Felteshobbies/moonlamp/firmware/tools/i18n_tests.py

"""German -> English replacements for the test scripts. Data table only."""

PAIRS = [
    # --- shared across the suite
    ('"Alle Pruefungen bestanden."', '"All checks passed."'),
    ('"FEHLGESCHLAGEN: %s" % ", ".join(FAILED)', '"FAILED: %s" % ", ".join(FAILED)'),
    ('"FEHLGESCHLAGEN: %d Pruefungen -> %s" % (len(FAILED), ", ".join(FAILED))',
     '"FAILED: %d checks -> %s" % (len(FAILED), ", ".join(FAILED))'),
    ('"FEHLER"', '"FAILED"'),
    ('"FEHLER: %r != %r"', '"FAILED: %r != %r"'),
    ('"  %-46s FEHLER: keine Anfrage verarbeitet"',
     '"  %-46s FAILED: no request was handled"'),

    # --- test_ephemeris.py
    ('"""Prueft die Ephemeride gegen bekannte astronomische Groessen.\n\n'
     'Laeuft am PC mit CPython, ohne Pico:\n'
     '    python firmware\\\\tests\\\\test_ephemeris.py\n"""',
     '"""Check the ephemeris against known astronomical quantities.\n\n'
     'Runs on a PC under CPython, no Pico needed:\n'
     '    python firmware\\\\tests\\\\test_ephemeris.py\n"""'),
    ('"1. Kalenderrechnung"', '"1. Calendar arithmetic"'),
    ('# J2000.0 ist per Definition der 1.1.2000 12:00 UT = JD 2451545.0',
     '# J2000.0 is by definition 2000-01-01 12:00 UT = JD 2451545.0'),
    ('"JD von 2000-01-01 12:00 UT"', '"JD of 2000-01-01 12:00 UT"'),
    ('# Rueckrechnung muss dasselbe Datum liefern',
     '# Converting back must give the same date'),
    ('"Hin- und Rueckrechnung %s"', '"round trip %s"'),
    ('"2. Sonne: Tagundnachtgleichen und Sonnenwenden"',
     '"2. Sun: equinoxes and solstices"'),
    ('# Zur Fruehlings-Tagundnachtgleiche ist die ekliptikale Laenge der Sonne 0 Grad,\n'
     '# zur Herbst-Tagundnachtgleiche 180. Die Termine sind kalendarisch bekannt.',
     '# At the March equinox the sun\'s ecliptic longitude is 0 degrees, at the\n'
     '# September equinox 180. The dates are known from the calendar.'),
    ('"Fruehlingsanfang 2026-03-20 14:46 UT"', '"March equinox 2026-03-20 14:46 UT"'),
    ('"Herbstanfang     2026-09-23 00:05 UT"', '"September equinox 2026-09-23 00:05 UT"'),
    ('"Sommersonnenwende 2026-06-21 08:24 UT"', '"June solstice 2026-06-21 08:24 UT"'),
    ('"Wintersonnenwende 2026-12-21 20:50 UT"', '"December solstice 2026-12-21 20:50 UT"'),
    ('"  %-46s Laenge %8.3f Grad, Abweichung %+6.3f  %s"',
     '"  %-46s longitude %8.3f deg, error %+6.3f  %s"'),
    ('"3. Mond: Bahngroessen ueber 20 Jahre"', '"3. Moon: orbital quantities over 20 years"'),
    ('"Entfernung Perigaeum..Apogaeum"', '"distance perigee..apogee"'),
    ('# Mittlere siderische Bewegung: 360 Grad in 27.32166 Tagen',
     '# Mean sidereal motion: 360 degrees in 27.32166 days'),
    ('"mittlere Bewegung in Laenge"', '"mean motion in longitude"'),
    ('"Grad/d"', '"deg/d"'),
    ('"4. Synodischer Monat und Langzeitdrift"', '"4. Synodic month and long-term drift"'),
    ('# Der Mittelwert weniger Lunationen taugt nicht als Mass: die Neumondzeiten\n'
     '# schwanken real um rund +/- 0,45 d um den gleichfoermigen Mittelwert, sodass\n'
     '# Anfang und Ende einer kurzen Reihe das Ergebnis dominieren. Aussagekraeftig\n'
     '# ist erst die Regressionssteigung ueber viele Lunationen.',
     '# The mean over a few lunations is not a useful measure: new moon instants\n'
     '# really do swing about +/- 0.45 d around the uniform mean, so the first and\n'
     '# last entry of a short series dominate the result. Only the regression\n'
     '# slope over many lunations is meaningful.'),
    ('"Streuung einzelner Lunationen"', '"spread of individual lunations"'),
    ('"Drift ueber %.0f Jahre, d pro Lunation"', '"drift over %.0f years, d per lunation"'),
    ('"physikalische Streuung der Neumondzeiten"',
     '"physical spread of new moon instants"'),
    ('"5. Beleuchtungsgrad an den Viertelpunkten"',
     '"5. Illuminated fraction at the quarter points"'),
    ('("Neumond", 0.0, 0.0, 0.005)', '("new moon", 0.0, 0.0, 0.005)'),
    ('("erstes Viertel", 0.25, 0.5, 0.02)', '("first quarter", 0.25, 0.5, 0.02)'),
    ('("Vollmond", 0.5, 1.0, 0.005)', '("full moon", 0.5, 1.0, 0.005)'),
    ('("letztes Viertel", 0.75, 0.5, 0.02)', '("last quarter", 0.75, 0.5, 0.02)'),
    ('"6. Vollmond kulminiert um Mitternacht (Gegenpunkt zur Sonne)"',
     '"6. Full moon culminates at midnight (opposite the sun)"'),
    ('# Bei Vollmond steht der Mond der Sonne gegenueber, geht also bei Sonnenuntergang\n'
     '# auf und kulminiert nahe der wahren Ortsmitternacht.',
     '# At full moon the moon is opposite the sun, so it rises at sunset and\n'
     '# culminates near true local midnight.'),
    ('"  Kulmination %5.2f h UT, wahre Ortsmitternacht %5.2f h UT, "',
     '"  culmination %5.2f h UT, true local midnight %5.2f h UT, "'),
    ('"Abweichung %+.2f h  %s"', '"error %+.2f h  %s"'),
    ('"Vollmond-Kulmination"', '"full moon culmination"'),
    ('"7. Sonnenhoehe: Mittagshoehe zur Sonnenwende"',
     '"7. Sun altitude: noon altitude at the solstice"'),
    ('# Am 21.6. steht die Sonne mittags 90 - Breite + 23.44 Grad hoch.',
     '# On 21 June the noon sun stands 90 - latitude + 23.44 degrees high.'),
    ('"Mittagshoehe am 21.6. bei 51.2 Grad Nord"',
     '"noon altitude on 21 June at 51.2 deg north"'),
    ('"Grad"', '"deg"'),
    ('# Duesseldorf, Beispielstandort', '# Duesseldorf, example location'),

    # --- test_render.py
    ('"""Prueft Bildaufbau und Dithering ohne Hardware.\n\n'
     '    python firmware\\\\tests\\\\test_render.py\n"""',
     '"""Check frame composition and dithering without hardware.\n\n'
     '    python firmware\\\\tests\\\\test_render.py\n"""'),
    ('"1. Bogenform und Kanten"', '"1. Arc shape and edges"'),
    ('"Bogen 0: alles aus"', '"arc 0: everything off"'),
    ('# Bei 180 Grad um Azimut 0 muessen die LEDs von -90 bis +90 Grad an sein',
     '# At 180 degrees around azimuth 0 the LEDs from -90 to +90 must be on'),
    ('"Bogen 180 Grad trifft die richtige Haelfte"',
     '"arc of 180 deg covers the correct half"'),
    ('# Weiche Kante: die aeussersten LEDs des Bogens muessen gedaempft sein',
     '# Soft edge: the outermost LEDs of the arc must be attenuated'),
    ('"weiche Bogenkanten vorhanden"', '"soft arc edges present"'),
    ('"%d gedaempfte LEDs" % len(edge)', '"%d attenuated LEDs" % len(edge)'),
    ('# Schmaler Bogen: Kante muss trotzdem mindestens einen LED-Abstand breit sein',
     '# Narrow arc: the edge must still be at least one LED pitch wide'),
    ('"schmalster Bogen hat mindestens eine LED"',
     '"narrowest arc still lights at least one LED"'),
    ('# Stetigkeit: beim Drehen des Azimuts darf keine LED springen',
     '# Continuity: no LED may jump as the azimuth is rotated'),
    ('"Azimut stufenlos drehbar"', '"azimuth rotates smoothly"'),
    ('"groesster Sprung pro 0,5 Grad: %.4f" % maxjump',
     '"largest step per 0.5 deg: %.4f" % maxjump'),
    ('# Dasselbe fuer die Bogenbreite ueber eine ganze Lunation',
     '# The same for the arc width across a whole lunation'),
    ('"Bogenbreite stufenlos"', '"arc width changes smoothly"'),
    ('"groesster Sprung pro 0,1 %% Phase: %.4f" % maxjump',
     '"largest step per 0.1 %% of phase: %.4f" % maxjump'),
    ('"2. Phasenzuordnung"', '"2. Phase mapping"'),
    ('"Bogen waechst monoton mit dem Beleuchtungsgrad"',
     '"arc grows monotonically with the illuminated fraction"'),
    ('"Vollmond ist der ganze Ring"', '"full moon is the whole ring"'),
    ('"Halbmond bei rund 174 Grad"', '"half moon at about 174 deg"'),
    ('"zunehmend wird von rechts beleuchtet"', '"waxing is lit from the right"'),
    ('"abnehmend wird von links beleuchtet"', '"waning is lit from the left"'),
    ('"3. Farbe"', '"3. Colour"'),
    ('"neutral: Weiss traegt alles"', '"neutral: white carries everything"'),
    ('"warmth 1: Rot dominiert, Weiss zurueck"', '"warmth 1: red dominates, white recedes"'),
    ('"Gamma: halbe Wahrnehmung ist rund ein Fuenftel Licht"',
     '"gamma: half the perceived level is about a fifth of the light"'),
    ('"4. Dithering"', '"4. Dithering"'),
    ('# Massstab ist die 8-Bit-Stufe: 256 Zaehler in 16-Bit-Aufloesung. Naives Runden\n'
     '# liefert bis zu einer halben Stufe Fehler, also 128. Alles deutlich darunter\n'
     '# heisst, dass die unteren Helligkeitsstufen nutzbar bleiben.',
     '# The yardstick is one 8-bit step: 256 counts at 16-bit resolution. Naive\n'
     '# rounding gives up to half a step of error, i.e. 128. Anything well below\n'
     '# that means the low brightness levels stay usable.'),
    ('"gleichmaessige Flaeche"', '"uniform area"'),
    ('"%.2f Stufen, naiv waeren 0,50" % (worst / STEP)',
     '"%.2f steps, naive would be 0.50" % (worst / STEP)'),
    ('# Ein Verlauf entlang des Rings, wie er an einer Bogenkante entsteht',
     '# A gradient along the ring, as it occurs at the edge of an arc'),
    ('"Verlauf entlang des Rings"', '"gradient along the ring"'),
    ('# Der Fehler darf sich ueber viele Frames nicht aufschaukeln',
     '# The error must not build up over many frames'),
    ('"kein Drift ueber 2000 Frames"', '"no drift over 2000 frames"'),
    ('"Mittel %.1f, Soll %d"', '"mean %.1f, target %d"'),

    # --- test_system.py
    ('"""Prueft Zeitzone, Konfiguration und die Programme ohne Hardware.\n\n'
     '    python firmware\\\\tests\\\\test_system.py\n"""',
     '"""Check time zone, configuration and the programs without hardware.\n\n'
     '    python firmware\\\\tests\\\\test_system.py\n"""'),
    ('"1. Sommerzeit nach EU-Regel"', '"1. Daylight saving time, EU rule"'),
    ('"2026-03-29 00:30 UTC noch Winterzeit"',
     '"2026-03-29 00:30 UTC is still standard time"'),
    ('"2026-10-25 00:30 UTC noch Sommerzeit"',
     '"2026-10-25 00:30 UTC is still summer time"'),
    ('"Mitte Juli ist Sommerzeit"', '"mid July is summer time"'),
    ('"Mitte Januar ist Winterzeit"', '"mid January is standard time"'),
    ('"letzter Sonntag Maerz 2026 ist der 29."',
     '"last Sunday in March 2026 is the 29th"'),
    ('"letzter Sonntag Oktober 2026 ist der 25."',
     '"last Sunday in October 2026 is the 25th"'),
    ('"Schaltjahr: letzter Sonntag Februar 2024 ist der 25."',
     '"leap year: last Sunday in February 2024 is the 25th"'),
    ('"2. Konfiguration"', '"2. Configuration"'),
    ('"unsinnige Werte werden begrenzt statt zu blockieren"',
     '"nonsense values get clamped instead of blocking"'),
    ('"Helligkeitsstufen steigen monoton"', '"brightness steps increase monotonically"'),
    ('"unterste Stufe unter einem Prozent"', '"lowest step is below one percent"'),
    ('"3. Programme liefern gueltige Frames"', '"3. Programs return valid frames"'),
    ('"4. P2 folgt dem echten Mond"', '"4. P2 follows the real moon"'),
    ('# Ueber 30 Tage in Stundenschritten: die Lampe darf nur dann leuchten, wenn\n'
     '# der Mond wirklich ueber dem Horizont steht.',
     '# Over 30 days in hourly steps: the lamp may only be lit while the moon is\n'
     '# genuinely above the horizon.'),
    ('        # Aus ist nur zulaessig, wenn der Mond unten steht, oder wenn bei Tag\n'
     '        # und Neumond schlicht nichts mehr uebrig ist, was 8 Bit darstellen\n'
     '        # koennten -- dann gaebe es real auch nichts zu sehen.',
     '        # Being off is only allowed when the moon is down, or when daylight\n'
     '        # and new moon leave nothing that 8 bits could represent -- in which\n'
     '        # case there would be nothing to see in reality either.'),
    ('"nie an, wenn der Mond unter dem Horizont steht"',
     '"never on while the moon is below the horizon"'),
    ('"%d von %d Stunden an"', '"%d of %d hours lit"'),
    ('"nie aus, solange real etwas zu sehen waere"',
     '"never off while something would really be visible"'),
    ('# Tagsueber deutlich gedimmt, nachts voll',
     '# Clearly dimmed during the day, full at night'),
    ('"tagsueber stark gedimmt gegenueber nachts"',
     '"strongly dimmed by day compared with night"'),
    ('"5. P1 braucht keinen Standort"', '"5. P1 needs no location"'),
    ('"P1 laeuft ohne Geodaten"', '"P1 runs without location data"'),

    # --- test_web.py
    ('"""Prueft, dass der HTTP-Server eine geteilte Anfrage vollstaendig liest.\n\n'
     'Der Fehler, den dieser Test festhaelt: Browser schicken Kopf und Rumpf eines\n'
     'POST regelmaessig in getrennten TCP-Segmenten. Ein einzelnes recv() liefert\n'
     'dann nur den Kopf, das Formular kommt leer an, und das Einrichtungsportal\n'
     'speichert stillschweigend nichts.\n\n'
     '    python firmware\\tests\\test_web.py\n"""',
     '"""Check that the HTTP server reads a split request completely.\n\n'
     'The bug this test pins down: browsers routinely send the head and the body\n'
     'of a POST in separate TCP segments. A single recv() then yields only the\n'
     'head, the form arrives empty, and the setup portal silently saves nothing.\n\n'
     '    python firmware/tests/test_web.py\n"""'),
    ('"1. POST mit Rumpf im zweiten Paket (der eigentliche Fehlerfall)"',
     '"1. POST with the body in a second packet (the actual failure case)"'),
    ('"geteilter POST"', '"split POST"'),
    ('# Rumpf bewusst spaeter', '# body deliberately later'),
    ('"Pfad"', '"path"'),
    ('"ssid mit Leerzeichen"', '"ssid containing a space"'),
    ('"Passwort prozentkodiert"', '"password percent-encoded"'),
    ('"Anzahl Felder"', '"number of fields"'),
    ('"2. POST in einem Stueck"', '"2. POST in one piece"'),
    ('"POST am Stueck"', '"single-packet POST"'),
    ('"3. GET mit Abfrageteil"', '"3. GET with a query string"'),
    ('"GET mit Query"', '"GET with query"'),
    ('"Pfad ohne Query"', '"path without the query"'),

    # --- calibrate_arc.py
    ('# Die Frontlippe des Rahmens verdeckt den aeusseren Ring, der zaehlt nicht mit',
     '# The frame\'s front lip hides the outer ring, so it does not count'),
    ('"""Bild fuer einen Lichtbogen, LED-Gewichte exakt wie in der Firmware."""',
     '"""Image for one arc of light, LED weights exactly as in the firmware."""'),
    ('"Kalibrierung der Bogenbreite  (H = %g mm konisch, LED z = %g mm, %d LEDs)"',
     '"Arc width calibration  (H = %g mm conical, LED z = %g mm, %d LEDs)"'),
    ('"  Bogen   scheinbarer Beleuchtungsgrad"',
     '"  arc     apparent illuminated fraction"'),
    ('# Monotonie sicherstellen, damit die Umkehrung eindeutig ist',
     '# Ensure monotonicity so that the inverse is unambiguous'),
    ('"Umkehrung: Beleuchtungsgrad -> Bogen (fuer ARC_TABLE in render.py)"',
     '"Inverse: illuminated fraction -> arc (for ARC_TABLE in render.py)"'),
    ('"Gegenprobe der aktuellen Tabelle in render.py:"',
     '"Cross-check of the current table in render.py:"'),
    ('"  Ziel    Tabelle sagt   gemessen ergibt"',
     '"  target  table says     measured gives"'),
    ('"  %.2f    %6.1f Grad    %.3f   %s"', '"  %.2f    %6.1f deg    %.3f   %s"'),
    ('"ABWEICHUNG"', '"DEVIATION"'),
    ('"groesste Abweichung: %.3f" % worst', '"largest deviation: %.3f" % worst'),

    # --- preview_firmware.py
    ('# Spektrum des W-Kanals eines SK6812 RGBW in Neutralweiss, als RGB-Anteil',
     '# Spectrum of an SK6812 RGBW white channel in neutral white, as RGB shares'),
    ('"""Ein Firmware-Frame (Liste von RGBW) in ein Farbbild der Lampe umrechnen."""',
     '"""Turn one firmware frame (a list of RGBW) into a colour image of the lamp."""'),
    ('# Eine echte Lunation in acht Schritten', '# One real lunation in eight steps'),
    ('"zunehmend" if p["waxing"]', '"waxing" if p["waxing"]'),
    ('else "abnehmend", p["illum"] * 100)', 'else "waning", p["illum"] * 100)'),
    ('"%s, %.0f %% beleuchtet"', '"%s, %.0f %% illuminated"'),
    ('"Eine Lunation, gerechnet aus echten Daten"',
     '"One lunation, computed from real dates"'),
    ('"Mondfinsternis"', '"lunar eclipse"'),
    ('"Vollmond, warmth = 0,9"', '"full moon, warmth = 0.9"'),
    ('"tiefstehender Mond"', '"low moon"'),
    ('"3/4, warmth = 0,5"', '"3/4, warmth = 0.5"'),
    ('"hochstehender Mond"', '"high moon"'),
    ('"3/4, coolness = 1,0"', '"3/4, coolness = 1.0"'),
    ('"Sichel mit Erdschein"', '"crescent with earthshine"'),
    ('"8 % beleuchtet, Erdschein 6 %"', '"8 % illuminated, earthshine 6 %"'),
    ('"Sichel ohne Erdschein"', '"crescent without earthshine"'),
    ('"8 % beleuchtet, zum Vergleich"', '"8 % illuminated, for comparison"'),
    ('"Nachtlicht P4"', '"night light P4"'),
    ('"voller Ring, 12 % Helligkeit, warm"', '"whole ring, 12 % brightness, warm"'),
    ('"Sonderzustaende und Farbe"', '"Special states and colour"'),
    ('"Rendere %d Bilder aus echter Firmware-Ausgabe ..." % len(scenes)',
     '"Rendering %d images from real firmware output ..." % len(scenes)'),
    ('"  [%2d/%2d] %-22s %2d LEDs an"', '"  [%2d/%2d] %-22s %2d LEDs on"'),
    ('"  Belichtung 1/%.3f" % ref', '"  exposure 1/%.3f" % ref'),
    ('"<title>Was die Firmware anzeigt</title>"',
     '"<title>What the firmware displays</title>"'),
    ('"<header class=\'wrap\'><p class=\'eyebrow\'>Durchgerechnet, nicht illustriert</p>"',
     '"<header class=\'wrap\'><p class=\'eyebrow\'>Computed, not illustrated</p>"'),
    ('"<h1>Was die Firmware anzeigt</h1>"', '"<h1>What the firmware displays</h1>"'),
    ('"<p class=\'lede\'>Jedes Bild entsteht aus der Kette Datum &rarr; Ephemeride "',
     '"<p class=\'lede\'>Every image comes out of the chain date &rarr; ephemeris "'),
    ('"&rarr; <code>render.phase_frame()</code> &rarr; 44 RGBW-Werte &rarr; "',
     '"&rarr; <code>render.phase_frame()</code> &rarr; 44 RGBW values &rarr; "'),
    ('"optisches Modell der Lampe. Die Bogenbreite je Phase stammt aus einer "',
     '"an optical model of the lamp. The arc width per phase comes from a "'),
    ('"Messung am echten Relief.</p></header><main class=\'wrap\'>"',
     '"measurement on the real relief.</p></header><main class=\'wrap\'>"'),
    ('"  geschrieben: %s" % hp', '"  written: %s" % hp'),
]
